mrWheel/deskAerosolSensor/assets/CO2_ConcentrationThresholds.png

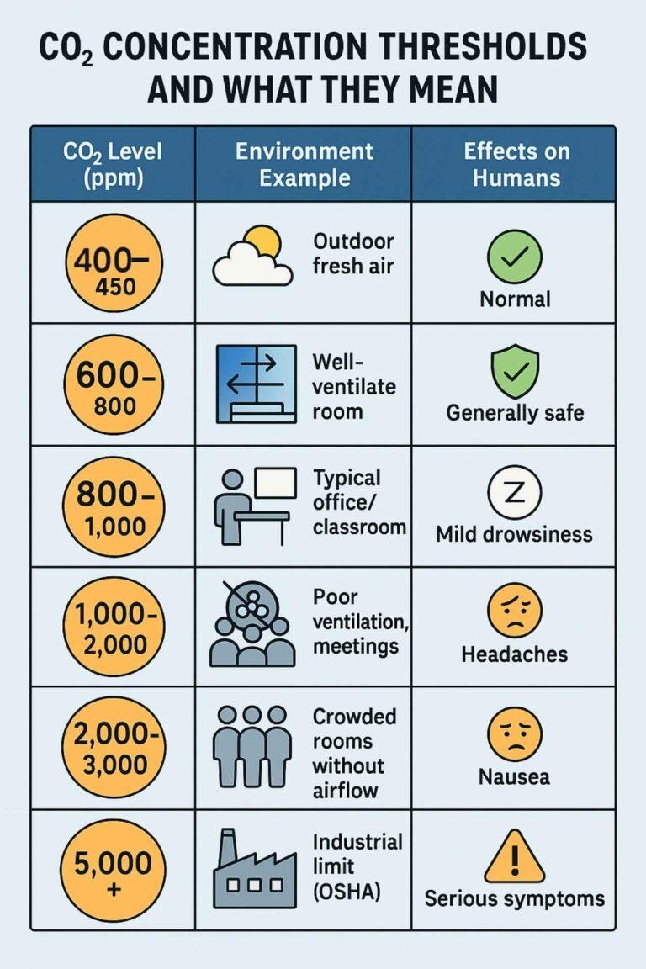
assets/CO2_ConcentrationThresholds.png
