mrWheel/deskAerosolSensor/assets/ILI9341_ESP32_Module_Size.png

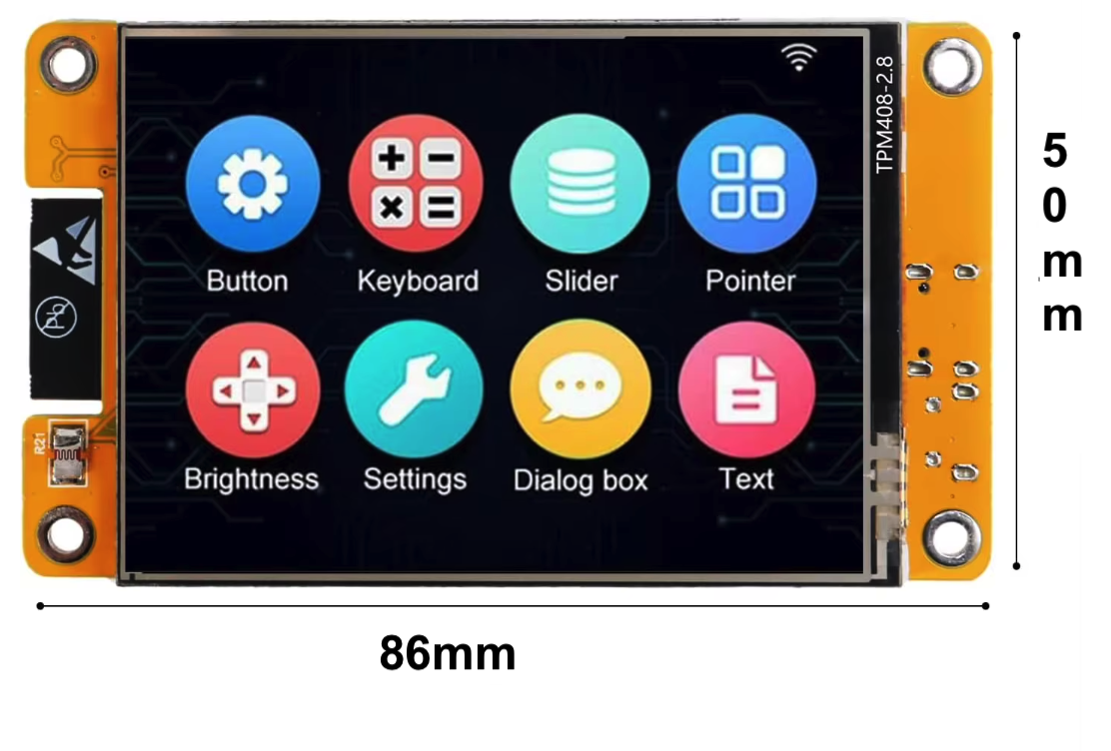
assets/ILI9341_ESP32_Module_Size.png
