mrWheel/deskAerosolSensor/assets/ParticulateMatter.png

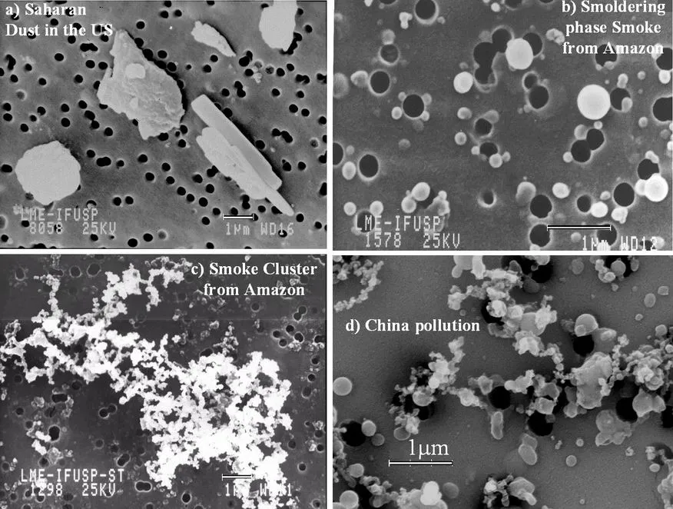
assets/ParticulateMatter.png
