mrWheel/deskAerosolSensor/src/colorScale.cpp

/*** Last Changed: 2026-03-29 - 13:32 ***/
#include "colorScale.h"

//--- Clamp floating point value to the range 0.0 .. 1.0
float clamp01(float value)
{
  if (value < 0.0f)
  {
    return 0.0f;
  }

  if (value > 1.0f)
  {
    return 1.0f;
  }

  return value;

} //   clamp01()

//--- Map a value from an input range to 0.0 .. 1.0 and clamp it
float mapRangeClamped(float value, float inMin, float inMax)
{
  if (inMax <= inMin)
  {
    return 0.0f;
  }

  return clamp01((value - inMin) / (inMax - inMin));

} //   mapRangeClamped()

//--- Approximate badness for PM1.0 / PM2.5 / PM4.0
float computePmBadness(float value)
{
  return mapRangeClamped(value, 0.0f, 55.4f);

} //   computePmBadness()

//--- Approximate badness for PM10
float computePm10Badness(float value)
{
  return mapRangeClamped(value, 0.0f, 154.0f);

} //   computePm10Badness()

//--- Approximate indoor ventilation badness for CO2
float computeCo2Badness(float value)
{
  return mapRangeClamped(value, 600.0f, 2000.0f);

} //   computeCo2Badness()

//--- Approximate relative badness for the Sensirion VOC index
float computeVocBadness(float value)
{
  return mapRangeClamped(value, 100.0f, 400.0f);

} //   computeVocBadness()

//--- Approximate relative badness for the Sensirion NOx index
float computeNoxBadness(float value)
{
  return mapRangeClamped(value, 1.0f, 300.0f);

} //   computeNoxBadness()

//--- Temperature color ramp: <=10C blue, 10..25C to red, >=25C full red
float computeTemperatureBadness(float value)
{
  if (value <= 10.0f)
  {
    return 0.0f;
  }

  if (value >= 25.0f)
  {
    return 1.0f;
  }

  return mapRangeClamped(value, 10.0f, 25.0f);

} //   computeTemperatureBadness()

//--- Approximate comfort badness for indoor humidity
float computeHumidityBadness(float value)
{
  if (value < 40.0f)
  {
    return mapRangeClamped(40.0f - value, 0.0f, 20.0f);
  }

  if (value > 60.0f)
  {
    return mapRangeClamped(value - 60.0f, 0.0f, 25.0f);
  }

  return 0.0f;

} //   computeHumidityBadness()

//--- Convert a badness score to a blue -> red color gradient
lv_color_t badnessToColor(float badness)
{
  badness = clamp01(badness);

  uint8_t red = 0;
  uint8_t green = 0;
  uint8_t blue = 0;

  if (badness < 0.5f)
  {
    const float t = badness / 0.5f;
    red = static_cast<uint8_t>(34.0f + ((250.0f - 34.0f) * t));
    green = static_cast<uint8_t>(211.0f + ((204.0f - 211.0f) * t));
    blue = static_cast<uint8_t>(238.0f + ((21.0f - 238.0f) * t));
  }
  else
  {
    const float t = (badness - 0.5f) / 0.5f;
    red = static_cast<uint8_t>(250.0f + ((239.0f - 250.0f) * t));
    green = static_cast<uint8_t>(204.0f + ((68.0f - 204.0f) * t));
    blue = static_cast<uint8_t>(21.0f + ((68.0f - 21.0f) * t));
  }

  return lv_color_make(red, green, blue);

} //   badnessToColor()
